9scarface11/Adjustable-Light-Bracket/parts/m5_bolt.SLDPRT

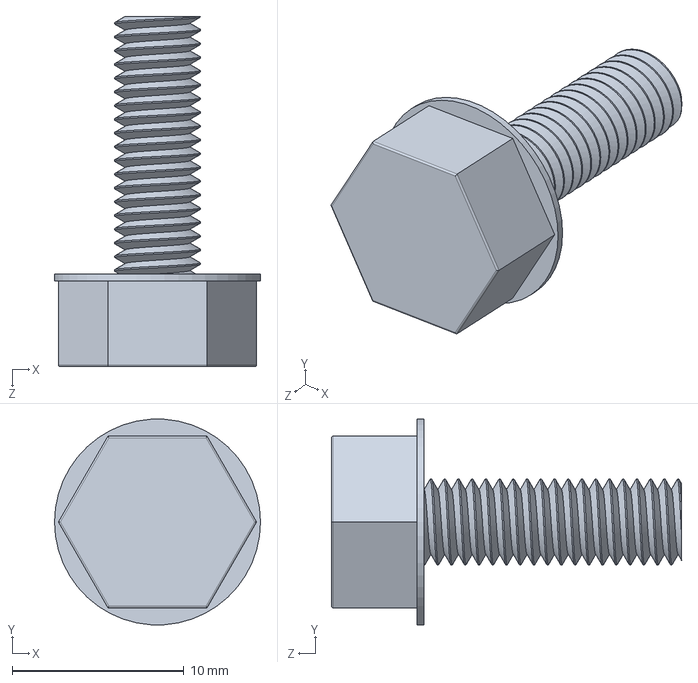
[picture p15: CAD file, 2026-07-23]
parts/m5_bolt.SLDPRT
12.0 x 12.0 x 20.4 mm
